unixjazz/bigdot/examples/monitor-ambiental-taina/private_settings.h

/************************* WiFi Access Point *********************************/
#define WLAN_SSID       ""                     // your network SSID
#define WLAN_PASS       ""                     // your network passwd

/************************* MQTT Set-Up ***************************************/
#define MQTT_SERVER       ""                   // endereco da mucua MQTT
#define MQTT_PORT         1883                 // porta na mucua MQTT
#define MQTT_CLIENT_ID    ""                   // nome da mucua movel
#define MQTT_USERNAME     ""                   // usuário na mucua MQTT
#define MQTT_PASSWD       ""	               // senha na mucua MQTT
