unixjazz/bigdot/examples/pms-wifi/private_settings.h

/************************* WiFi Access Point *********************************/
#define WLAN_SSID  "NAME" // your network SSID (name)
#define WLAN_PASS  "PASSWORD" // your network password
/************************* Adafruit.io Setup *********************************/
#define AIO_SERVER      "io.adafruit.com"
#define AIO_SERVERPORT  1883
// visit io.adafruit.com if you need to create an account,
// or if you need your Adafruit IO key.
#define AIO_USERNAME    "USERNAME"
#define AIO_KEY         "KEY"
