unixjazz/bigdot/examples/ttn-pm-co2/ttn-credentials.h

/*
 *
 * Things Network credentials
 *
 */

// dev id (LSB)
static const u1_t PROGMEM DEVEUI[8]= { };

// application id (LSB)
static const u1_t PROGMEM APPEUI[8]= { };

// application key (MSB)
static const u1_t PROGMEM APPKEY[16] = { };
